JonasHeselschwerdt/ChatGPT-mod-for-calculators/Documentation/MainboardV1/File structure description.pdf

File structure

UI.c + UI.h

Base functions: Directly
control the GPIOs of the
ESP32

Advanced functions:
Perform multiple Base
functions

Externally used
functions: Called in main.c

Network.c / Network.h

Wifi / NVS / OpenAI

Features: Up to 8 Wifi Credentials can be saved (non volatile).
An API Key for OpenAI can be saved (non volatile).
Automatic Wifi reconnection try upon disconnect: Wifi list (1-8) gets scanned, first available Wifi gets chosen)
Send Messages to OpenAI and return answer

Keyset.c + Keyset.h

▶

Lookup - Tables for the LCD and the Keypad Matrix
