JonasHeselschwerdt/ChatGPT-mod-for-calculators/Documentation/MainboardV1/Keyboard Layout.pdf

## SMzur

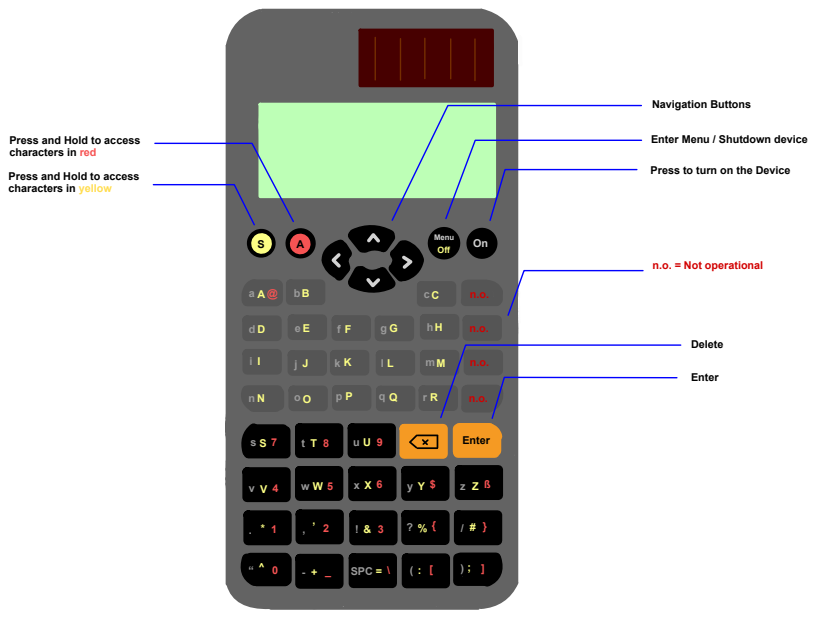
[picture p16: page 1]
- SPC; Enter; Menu; Navigation Buttons; Enter Menu / Shutdown device; Delete; n.o. = Not operational; Off ·&; for ↓ar

Press and Hold to access
characters in red

characters in yellow

Press to turn on the Device
