JonasHeselschwerdt/ChatGPT-mod-for-calculators/Documentation/MainboardV1/Board stackup description.pdf

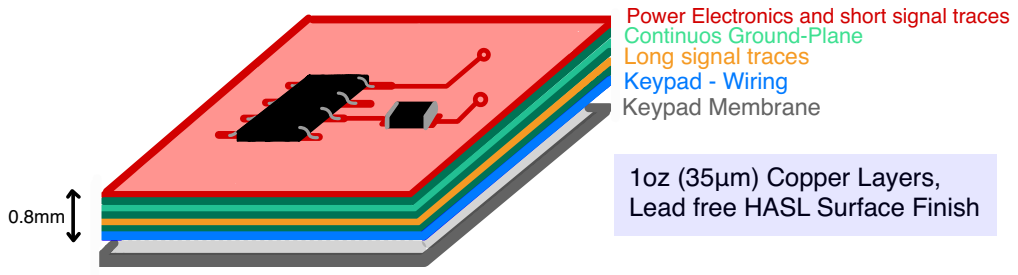
[picture p17: page 1]
1oz (35μm) Copper Layers,

Power Electronics and short signal traces
Continuos Ground-Plane
Long signal traces
Keypad - Wiring
Keypad Membrane

Lead free HASL Surface Finish m-
