JonasHeselschwerdt/ChatGPT-mod-for-calculators/Documentation/MainboardV2_0_2/DigitalSilkscreenMainboardV202.pdf

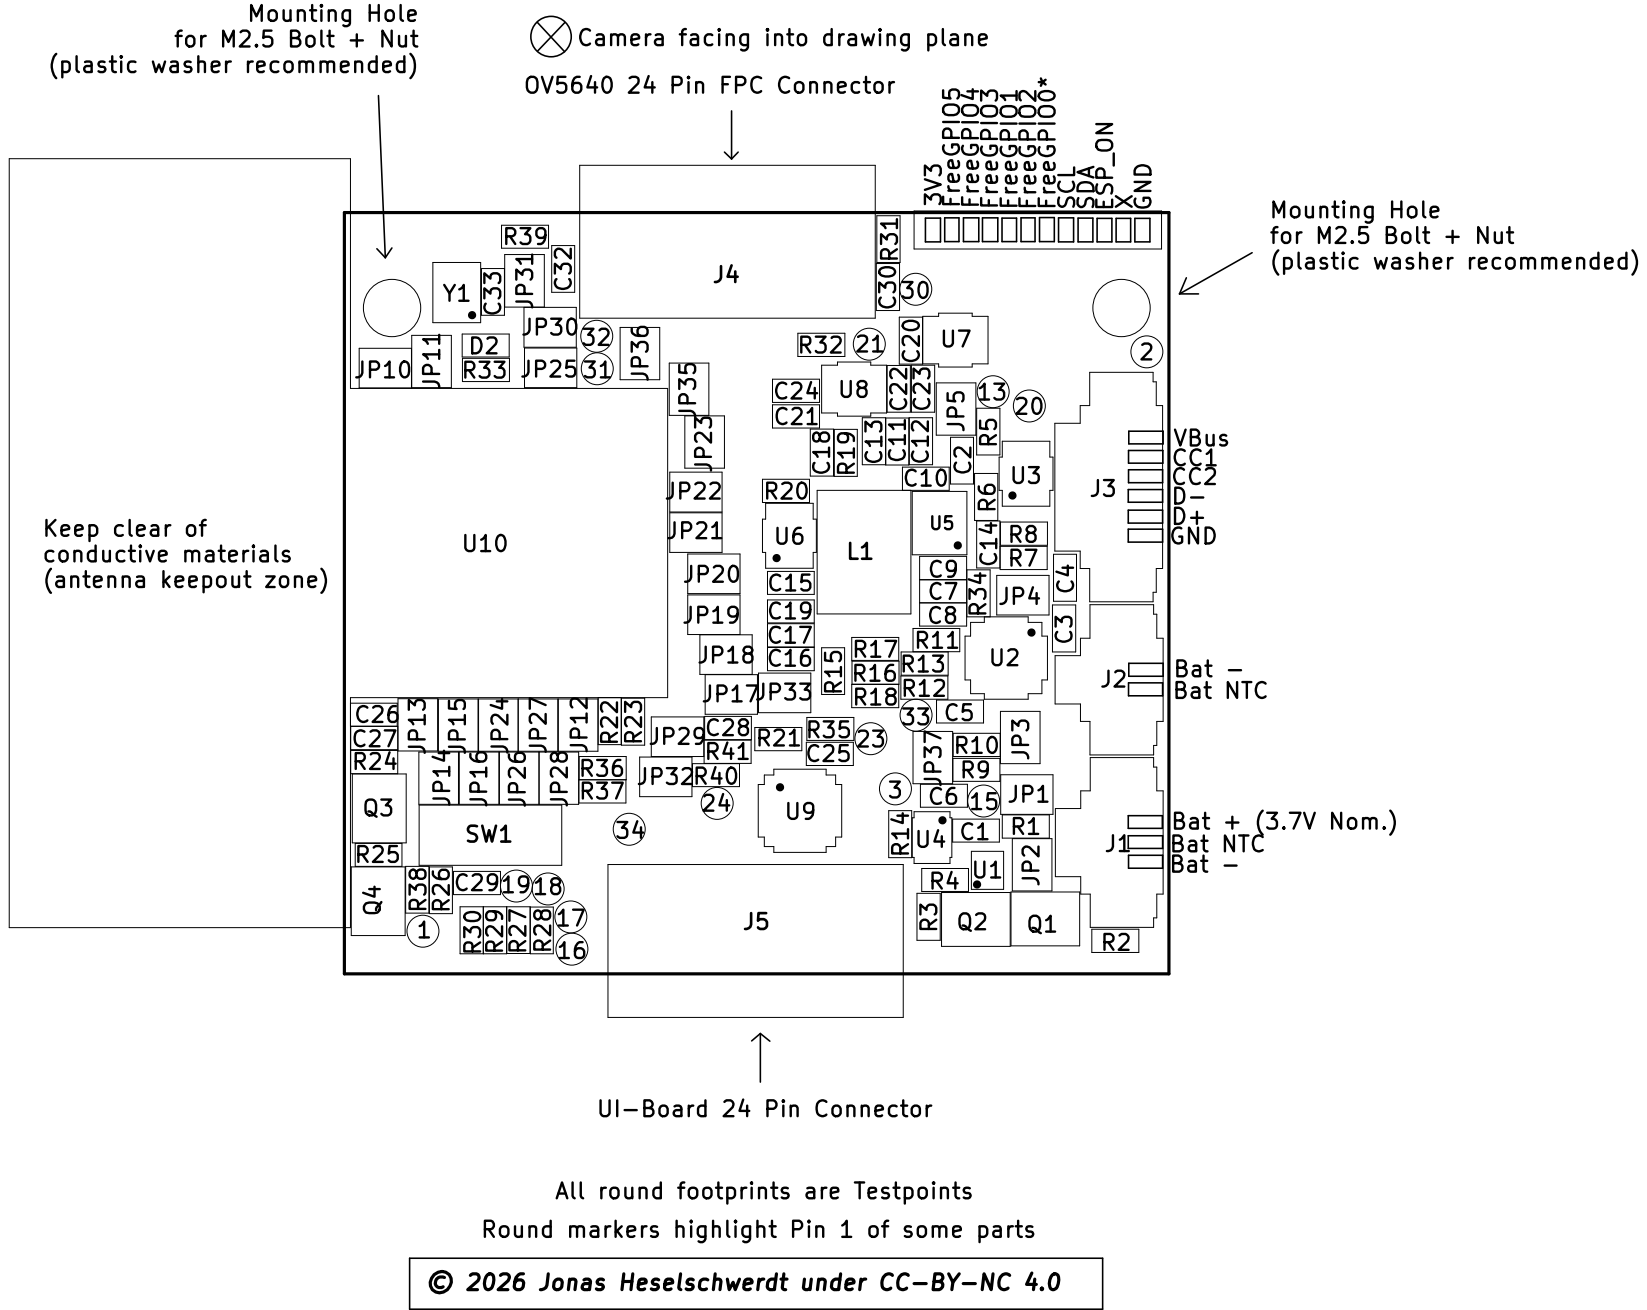
[picture p21: page 1]
