JonasHeselschwerdt/ChatGPT-mod-for-calculators/Software_MainboardV2/main/Source/AI_calc_device.c

/*

ChatGPT Hardware Hack for calculators: Software V2

© 2026 Jonas Heselschwerdt
Licensed under GPLv3 

device.c: GPIO, I2C, and other connectivity

*/

// #region Includes

/*
#########################################################################################
##                                                                                     ##
##  Includes                                                                           ##
##                                                                                     ##
#########################################################################################
*/

#include "driver/i2c_master.h"
#include "driver/gpio.h"
#include "esp_log.h"
#include "freertos/FreeRTOS.h"
#include "nvs_flash.h"
#include "nvs.h"

#include "AI_calc_main.h"
#include "AI_calc_device.h"
#include "AI_calc_maindisplay.h"
#include "AI_calc_keypad.h"
#include "AI_calc_battery.h"
#include "AI_calc_sidedisplay.h"
#include "AI_calc_network.h"
#include "AI_calc_camera.h"
    
// #endregion

// #region Static variables

/*
#########################################################################################
##                                                                                     ##
##   Static variables                                                                  ##
##                                                                                     ##
#########################################################################################
*/

char* shutdown_text[MAIN_DISPLAY_ROWS] = {
    STYLE_LINE,
    "  Device is         ",
    "  shutting down     ",
    STYLE_LINE
};

static nvs_handle_t device_settings_handle;

// #endregion

// #region Extern variables

/*
#########################################################################################
##                                                                                     ##
##   Extern variabels                                                                  ##
##                                                                                     ##
#########################################################################################
*/

i2c_master_bus_handle_t i2c_bus = NULL;

device_TypeDef device;

// #endregion

// #region Static function declarations

/*
#########################################################################################
##                                                                                     ##
##   Static function declarations                                                      ##
##                                                                                     ##
#########################################################################################
*/
static void i2c_bus_init(void);

static void gpios_init(void);
static void gpios_set_default(void);
static void free_gpios_init(void);

static void nvs_init(void);
static void nvs_get_device_infos(void);
static void nvs_save_device_infos(void);

// #endregion

// #region Static functions

/*
#########################################################################################
##                                                                                     ##
##   Static functions                                                                  ##
##                                                                                     ##
#########################################################################################
*/

static void i2c_bus_init(void){

    i2c_master_bus_config_t i2c_config = {
        .clk_source = I2C_CLK_SRC_DEFAULT,
        .i2c_port = I2C_NUM_0,
        .sda_io_num = SDA,
        .scl_io_num = SCL,
        .glitch_ignore_cnt = 7,
        .flags.enable_internal_pullup = false       // external resistors R27:28 on board
    };
    ESP_ERROR_CHECK(i2c_new_master_bus(&i2c_config, &i2c_bus));
}


static void gpios_init(void){

    uint64_t outputs = 0;
    outputs |= (1ULL << ESP_N_POWERLATCH);
    outputs |= (1ULL << MAIN_DISPLAY_N_RESET);
    outputs |= (1ULL << TCA8418_N_RESET);
    outputs |= (1ULL << SIDE_DISPLAY_N_RESET);
    outputs |= (1ULL << CAMERA_POWER_ENABLE);
    gpio_config_t output_config = {
        .pin_bit_mask = outputs,
        .mode = GPIO_MODE_OUTPUT,
        // Pullups/Pulldowns externally on board (R35:37 + R19)
        .pull_up_en = GPIO_PULLUP_DISABLE,
        .pull_down_en = GPIO_PULLDOWN_DISABLE,
        .intr_type = GPIO_INTR_DISABLE
    };
    gpio_config(&output_config);

    uint64_t inputs = 0;
    inputs |= (1ULL << TCA8418_N_INTERRUPT);
    gpio_config_t input_config = {
        .pin_bit_mask = inputs,
        .mode = GPIO_MODE_INPUT,
        .pull_up_en = GPIO_PULLUP_DISABLE,
        .pull_down_en = GPIO_PULLDOWN_DISABLE,
        .intr_type = GPIO_INTR_DISABLE
    };
    gpio_config(&input_config);

    uint64_t disabled = 0;
    disabled |= (1ULL << BMS_NTC_VOLTAGE_DIV_ACT);
    gpio_config_t disable_config = {
        .pin_bit_mask = disabled,
        .mode = GPIO_MODE_DISABLE,
        .pull_up_en = GPIO_PULLUP_DISABLE,
        .pull_down_en = GPIO_PULLDOWN_DISABLE,
        .intr_type = GPIO_INTR_DISABLE
    };
    gpio_config(&disable_config);
}

static void gpios_set_default(void){

    // Turns off both displays, TCA8418, camera and turn on ESP powerlatch circuit
    gpio_set_level(ESP_N_POWERLATCH,0);
    gpio_set_level(TCA8418_N_RESET,0);
    gpio_set_level(SIDE_DISPLAY_N_RESET,0);
    gpio_set_level(MAIN_DISPLAY_N_RESET,0);
    gpio_set_level(CAMERA_POWER_ENABLE,0);
}

static void free_gpios_init(void){

    // Not used by default, configure as Inputs with internal Pullups
    uint64_t freegpios = 0;
    freegpios |= (1ULL << FREEGPIO_5);
    freegpios |= (1ULL << FREEGPIO_4);
    freegpios |= (1ULL << FREEGPIO_3);
    freegpios |= (1ULL << FREEGPIO_2);
    freegpios |= (1ULL << FREEGPIO_1);

    gpio_config_t freegpio_config = {
        .pin_bit_mask = freegpios,
        .mode = GPIO_MODE_INPUT,
        .pull_up_en = GPIO_PULLUP_ENABLE,
        .pull_down_en = GPIO_PULLDOWN_DISABLE,
        .intr_type = GPIO_INTR_DISABLE
    };
    gpio_config(&freegpio_config);
}

static void nvs_init(void){

    // Inits nvs for later use
    esp_err_t err = nvs_flash_init();
    if (err == ESP_ERR_NVS_NO_FREE_PAGES || err == ESP_ERR_NVS_NEW_VERSION_FOUND){
        ESP_ERROR_CHECK(nvs_flash_erase());
        err = nvs_flash_init();
    }
    ESP_ERROR_CHECK(err);
}

static void nvs_get_device_infos(void){

    // Called during init sequence
    // Open device namespace
    ESP_ERROR_CHECK(nvs_open("device", NVS_READWRITE, &device_settings_handle));
    if (nvs_get_u8(device_settings_handle,"debugmode",&device.debug_mode) != ESP_OK){
        device.debug_mode = DEVICE_DEFAULT_DEBUG;
    }
    if (nvs_get_u8(device_settings_handle,"maindis_contr",&device.main_display_contrast) != ESP_OK){
        device.main_display_contrast = DEVICE_DEFAULT_MAINDIS_CONTR;
    }
    if (nvs_get_u8(device_settings_handle,"sidedis_contr",&device.side_display_contrast) != ESP_OK){
        device.side_display_contrast = DEVICE_DEFAULT_SIDEDIS_CONTR;
    }
    size_t name_length = sizeof(device.name);
    if (nvs_get_str(device_settings_handle,"name",device.name,&name_length) != ESP_OK){
        strcpy(device.name,DEVICE_DEFAULT_NAME);
    }
}

static void nvs_save_device_infos(void){

    // Save infos about device into NVS
    // Called upon shutdown

    // Error state not checked, if reading fails during next init default values are chosen
    nvs_set_u8(device_settings_handle,"debugmode",device.debug_mode);
    nvs_set_u8(device_settings_handle,"maindis_contr",device.main_display_contrast);
    nvs_set_u8(device_settings_handle,"sidedis_contr",device.side_display_contrast);
    nvs_set_str(device_settings_handle,"name",device.name);
    nvs_commit(device_settings_handle);
}

// #endregion

// #region Extern functions

/*
#########################################################################################
##                                                                                     ##
##    Extern functions                                                                 ##
##                                                                                     ##
#########################################################################################
*/

void powerlatch_shutdown(void){

    // turns off device properly and informs user
    nvs_save_device_infos();
    dogm204_display_control(DOGM204_CURSOR_OFF_BIT|DOGM204_CURSOR_NO_BLINK_BIT|DOGM204_DISPLAY_ON_BIT);
    dogm204_print_screen(shutdown_text);
    vTaskDelay(pdMS_TO_TICKS(1000));
    gpio_set_level(ESP_N_POWERLATCH,1);
}

void powerlatch_shutdown_immediately(void){

    // turns off device 
    gpio_set_level(ESP_N_POWERLATCH,1);
}

void device_init(void){

    // GPIOs
    gpios_init();
    free_gpios_init();
    gpios_set_default();
    // I2C
    i2c_bus_init();
    // Get device informations from NVS
    // before peripherals are initialized
    nvs_init();
    nvs_get_device_infos();
    // Keypad and more GPIOs
    tca8418_init_keypad();
    tca8418_init_gpios();
    // Main display
    dogm204_init();
    dogm204_clear_screen();
    // Sidedisplay
    dep128064_init();
    dep128064_clear_screen();
    device.side_display_on = 0;
    // BMS
    uint8_t bms_initial_state = bms_init();
    if (bms_initial_state != BMS_OK){
        dogm204_print_error_screen(bms_error_strings[bms_initial_state],ERROR_SOURCE_BMS);
        vTaskDelay(pdMS_TO_TICKS(500));
        powerlatch_shutdown_immediately();
    }
    // Camera
    camera_init();
    // Wifi
    wifi_init();
}

// #endregion
