JonasHeselschwerdt/ChatGPT-mod-for-calculators/Software_MainboardV2/main/Include/AI_calc_main.h

/*

ChatGPT Hardware Hack for calculators: Software V2

© 2026 Jonas Heselschwerdt
Licensed under GPLv3 

main.h: Project config settings

*/

#ifndef MAIN_H
#define MAIN_H

// Includes






// Software- Version Information, Strings should have the same length as MAIN_DISPLAY_COLUMNS!

#define SOFTWARE_VERSION_STRING         "Software: v.2.0.0   "
#define HARDWARE_VERSION_STRING         "Hardware: v.2.0.3   "      // also works with v2.0.1 and v2.0.2 
                                                                    // (with some restrictions, see changelog)
#define DEVICE_STATUS_STRING            "Status: Prototype   "






#endif
