JonasHeselschwerdt/ChatGPT-mod-for-calculators/Software_MainboardV2/main/Include/AI_calc_user_extension.h

/*

ChatGPT Hardware Hack for calculators: Software V2

© 2026 Jonas Heselschwerdt
Licensed under GPLv3 

user_extension.h: Write code for user extensions here

*/

/*

How to setup user extensions:

1) Make your hardware changes (for example via the Kicad User Extension Board template project)
2) Setup the FreeGPIOs (FREEGPIO_5...1 in device.h and device.c and FREEGPIO_0 in keypad.c and keypad.h)
   (use FREEGPIO_0 for slower signals ideally)
3) Configure your custom software module in this file
4) Integrate it into the user interface in UI.c

*/
